Matheus21sousa/WeatherStation/3D_Parts/WS - Suporte abrigo met. .3mf

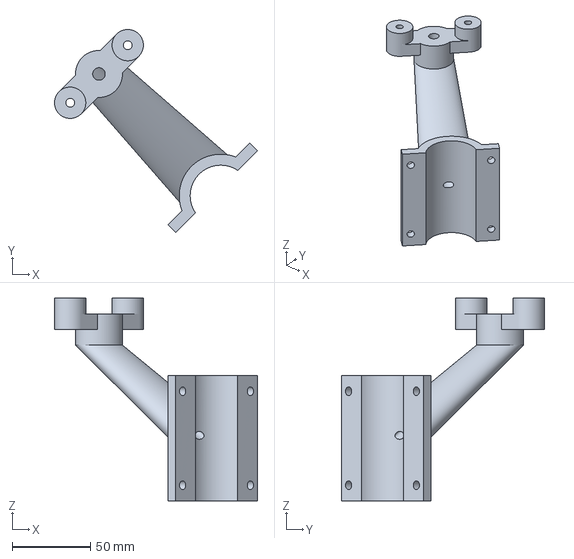
[picture p15: CAD file, 2023-11-15]
3D_Parts/WS - Suporte abrigo met. .3mf
129.6 x 129.6 x 129.5 mm
